sjgray/B1024/board pics/B1024-Bare-Bottom.jpg

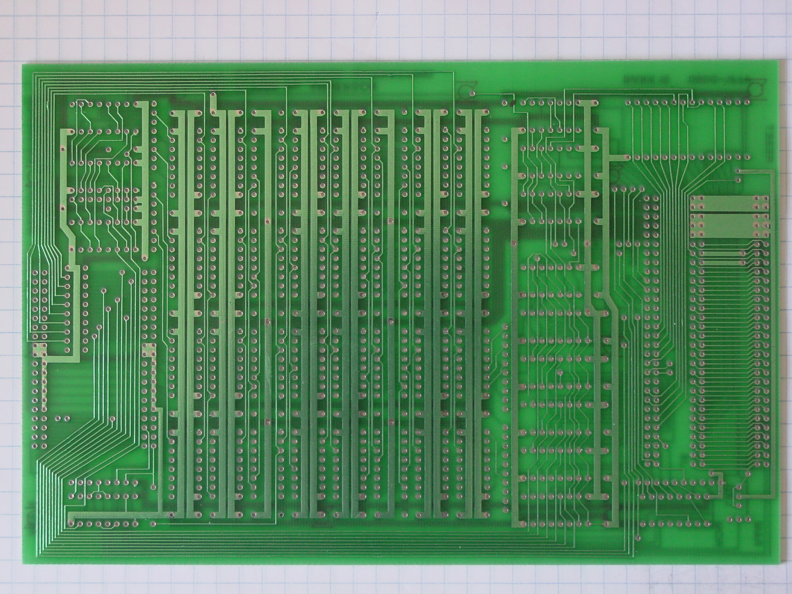
board pics/B1024-Bare-Bottom.jpg
